avivco5/juckbox/design/4f1e619b-26d6-46fd-890a-413171e89c38.png

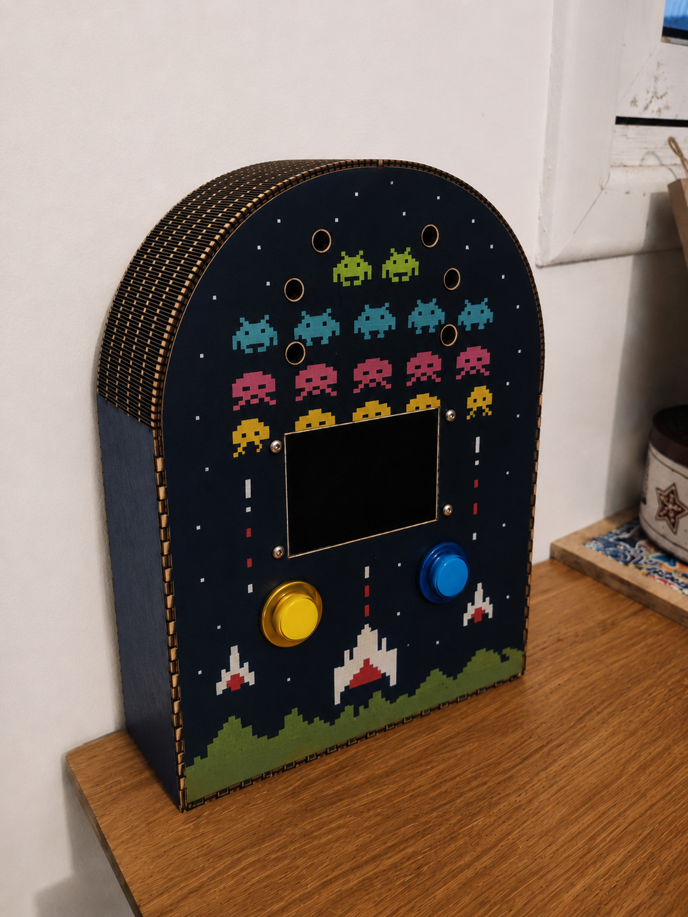
design/4f1e619b-26d6-46fd-890a-413171e89c38.png
