avivco5/juckbox/design/27ebfebb-9b08-406d-80b3-61969d63497d.png

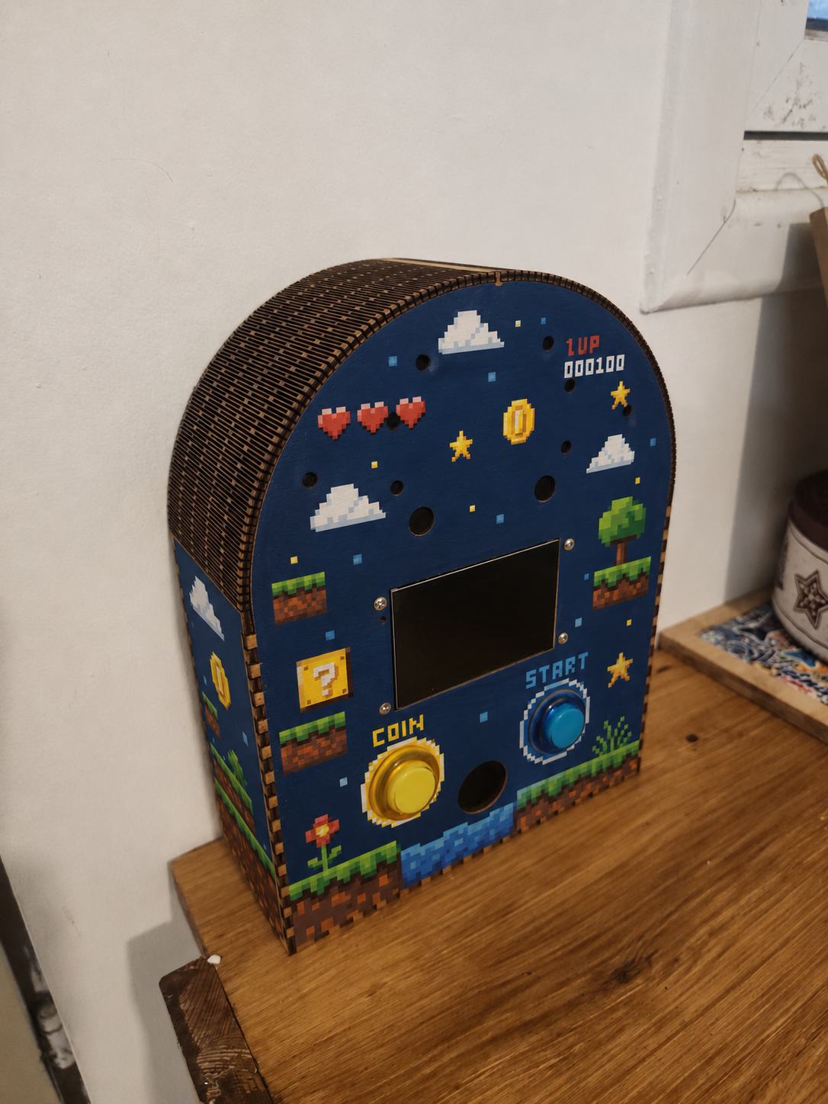
design/27ebfebb-9b08-406d-80b3-61969d63497d.png
