avivco5/juckbox/design/34f83e39-5371-48dc-b8f7-de62b93157a2.png

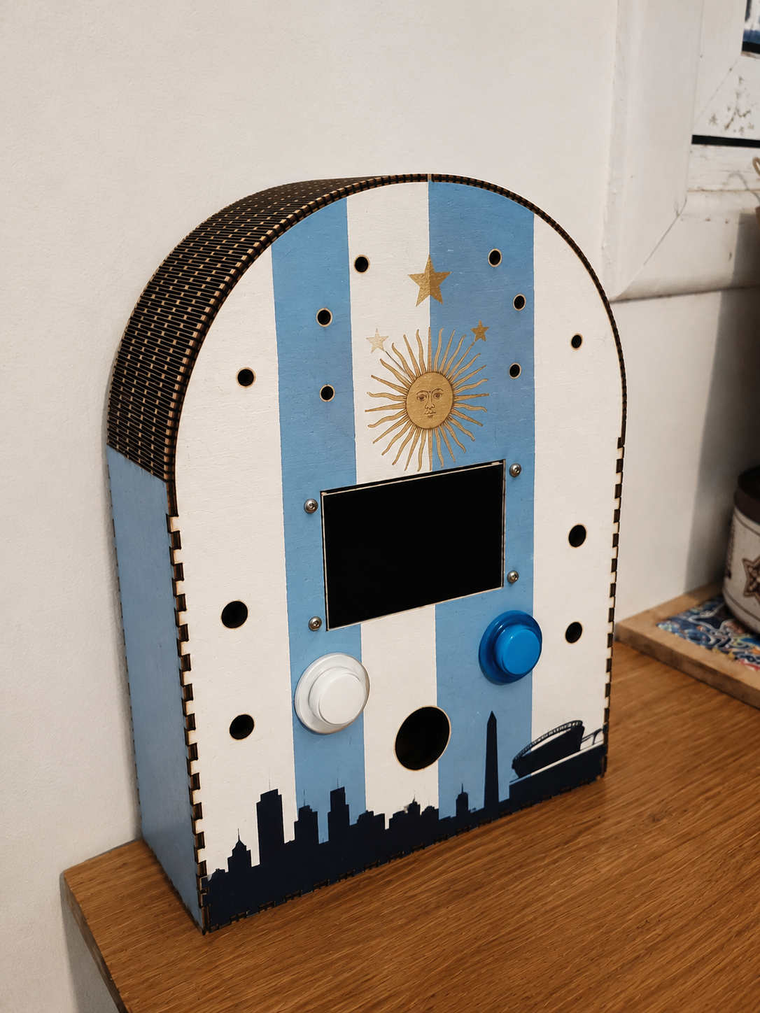
design/34f83e39-5371-48dc-b8f7-de62b93157a2.png
