avivco5/juckbox/design/97b78420-3eb2-440e-917a-7a141fbbd64f.png

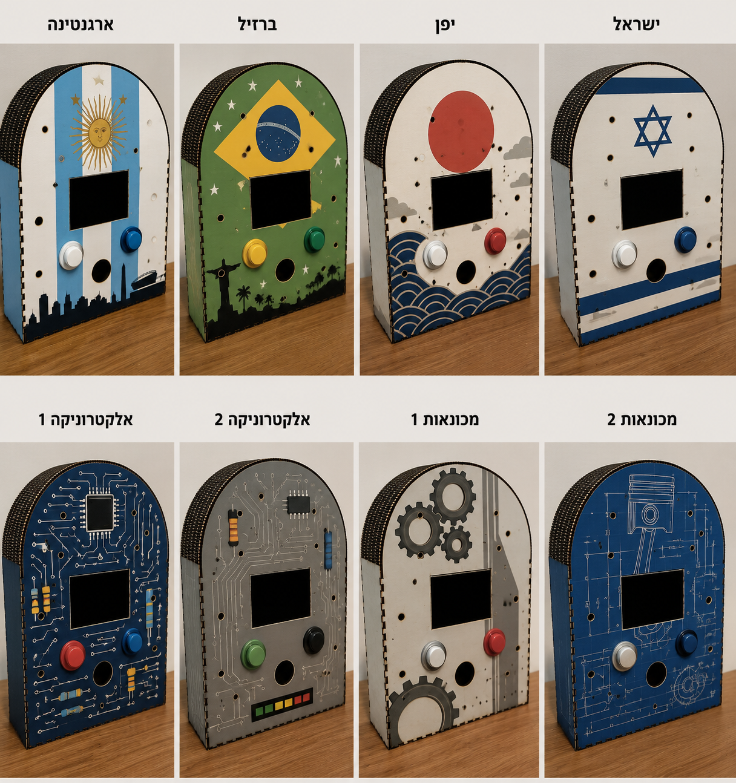
design/97b78420-3eb2-440e-917a-7a141fbbd64f.png
