avivco5/juckbox/design/892bf61c-9726-4b2f-9761-84908b169551.png

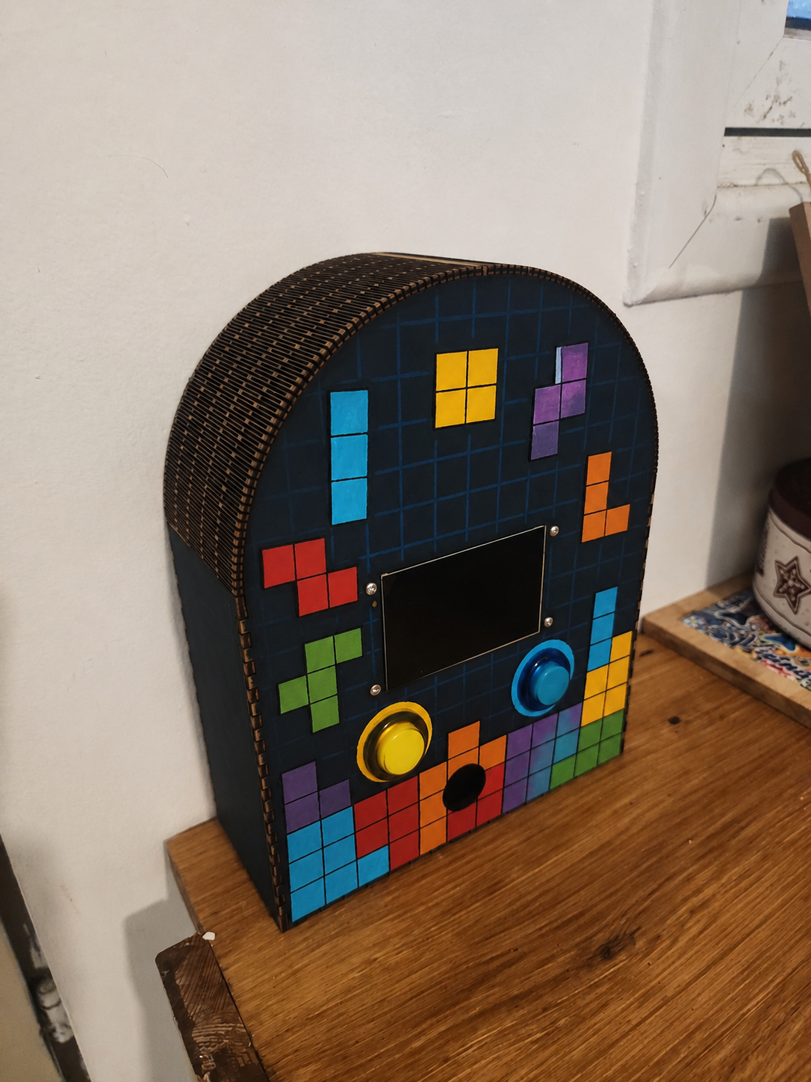
design/892bf61c-9726-4b2f-9761-84908b169551.png
