avivco5/juckbox/design/26971b3d-81b3-4ab2-a4b9-a8ff20f6ef65.png

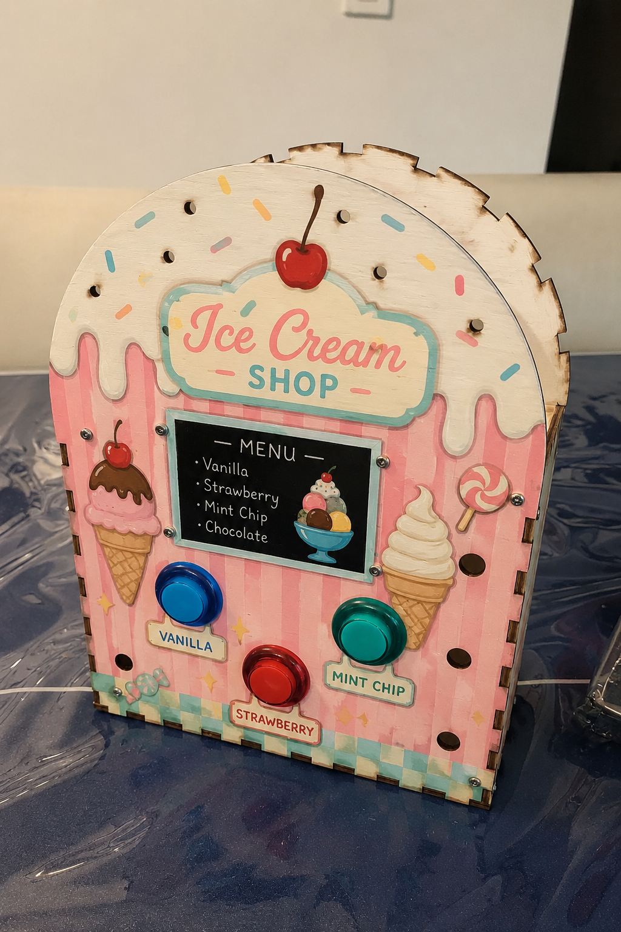
design/26971b3d-81b3-4ab2-a4b9-a8ff20f6ef65.png
