avivco5/juckbox/design/bb11b732-9e90-4e72-ab10-1f3d75999959.png

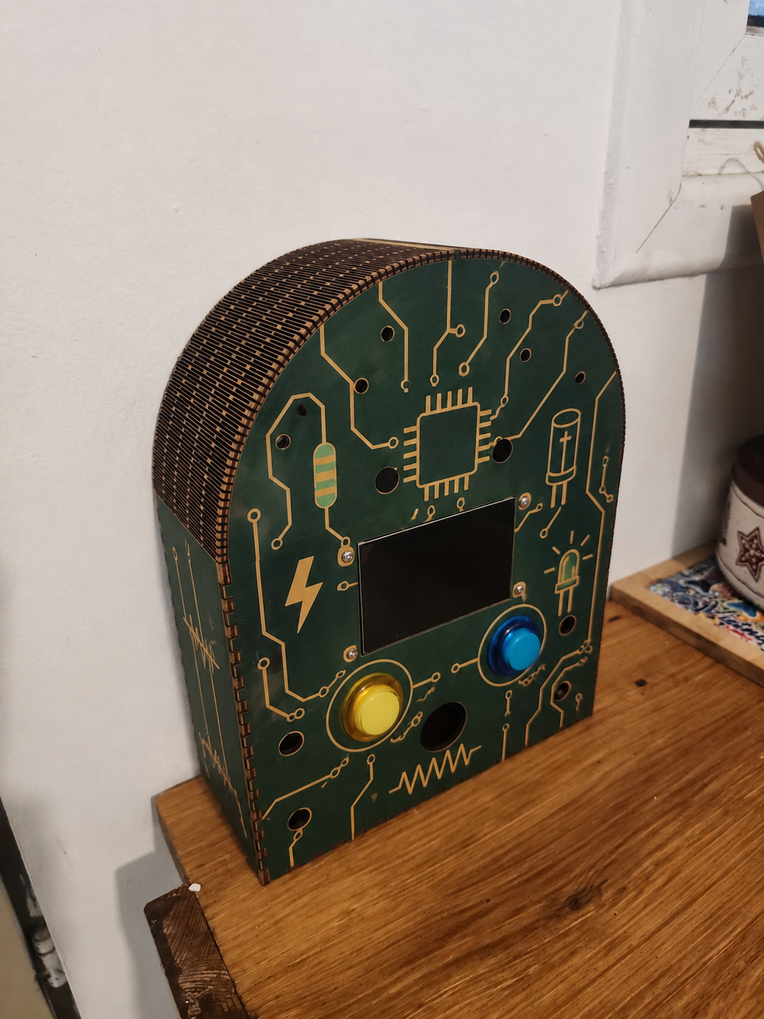
design/bb11b732-9e90-4e72-ab10-1f3d75999959.png
