avivco5/juckbox/design/ChatGPT Image Jul 7, 2026, 10_58_40 PM.png

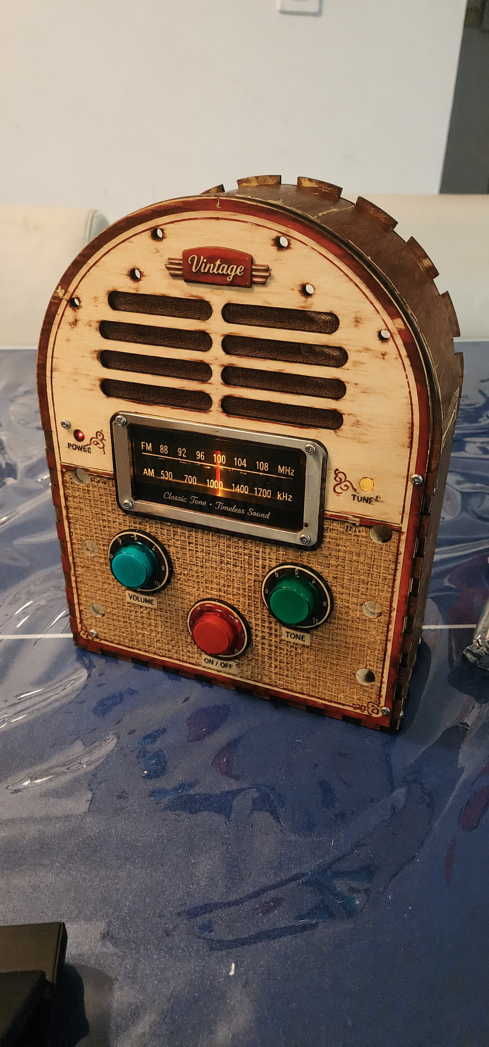
design/ChatGPT Image Jul 7, 2026, 10_58_40 PM.png
