avivco5/juckbox/design/ChatGPT Image Jul 7, 2026, 11_04_46 PM.png

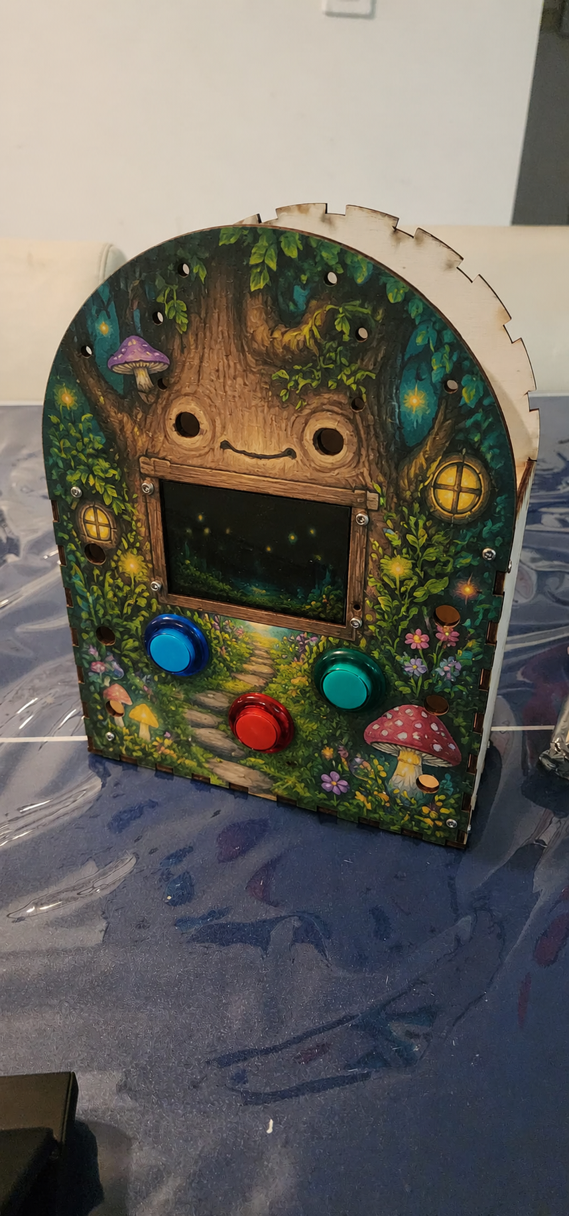
design/ChatGPT Image Jul 7, 2026, 11_04_46 PM.png
