avivco5/juckbox/design/ChatGPT Image Jul 11, 2026, 03_16_33 PM.png

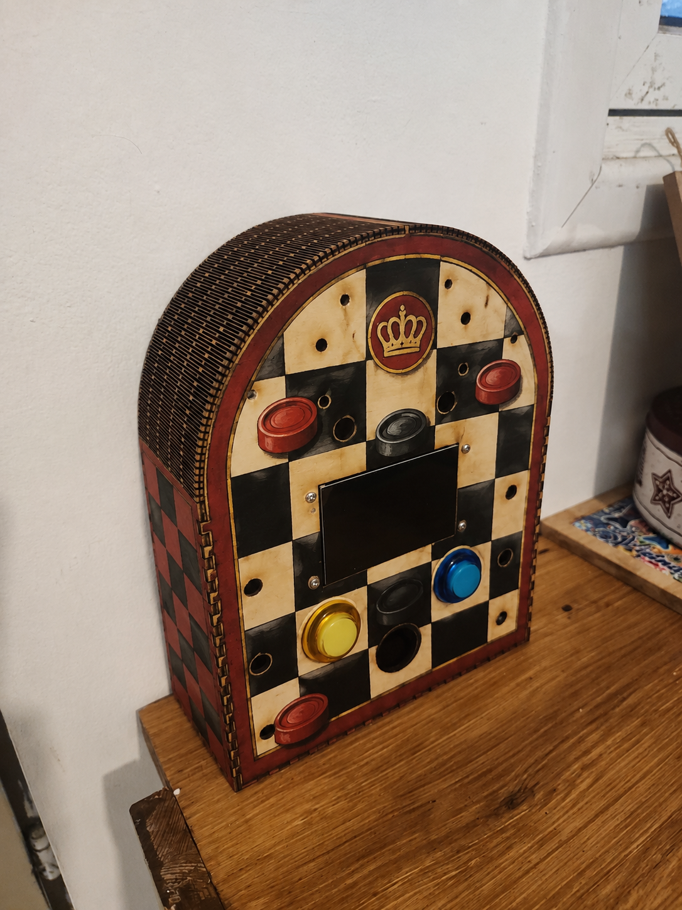
design/ChatGPT Image Jul 11, 2026, 03_16_33 PM.png
