avivco5/juckbox/design/ChatGPT Image Jul 13, 2026, 04_00_38 AM.png

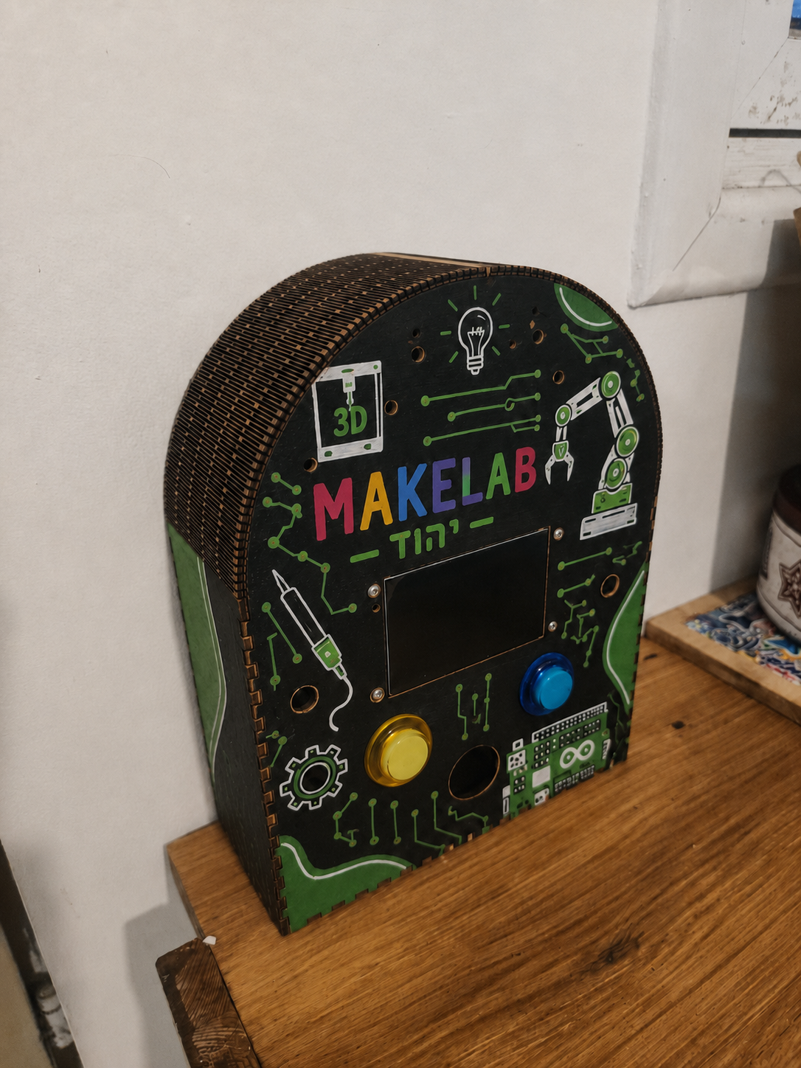
design/ChatGPT Image Jul 13, 2026, 04_00_38 AM.png
