avivco5/juckbox/design/d009f1e1-ca12-4269-a878-5f64a306e6af.png

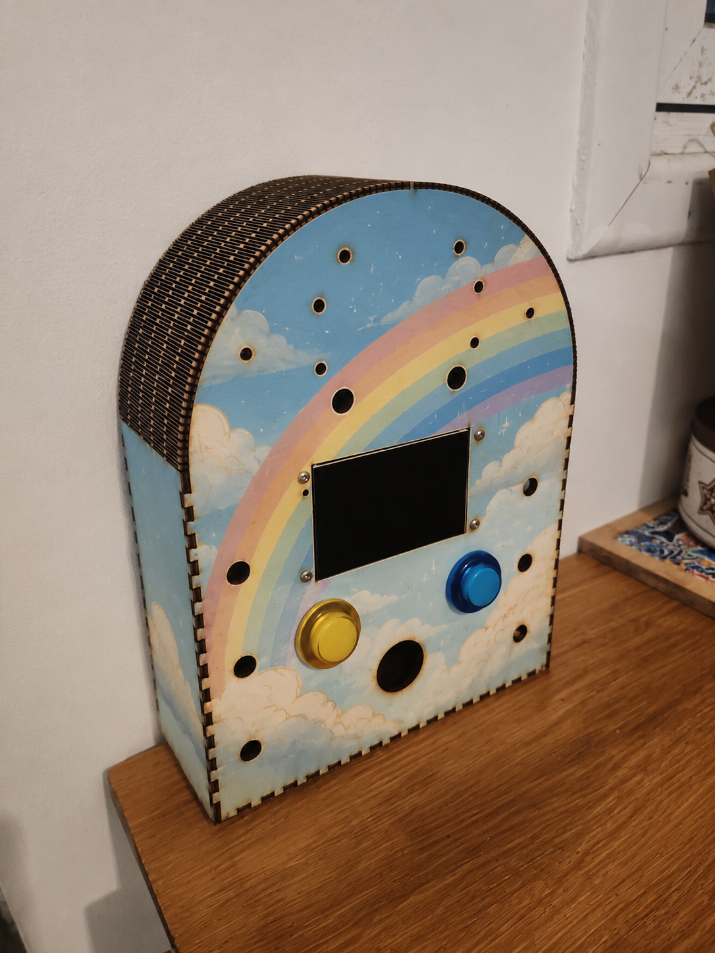
design/d009f1e1-ca12-4269-a878-5f64a306e6af.png
