avivco5/juckbox/design/f1ebbad3-cf48-4e45-876e-ef45e3f0cdeb.png

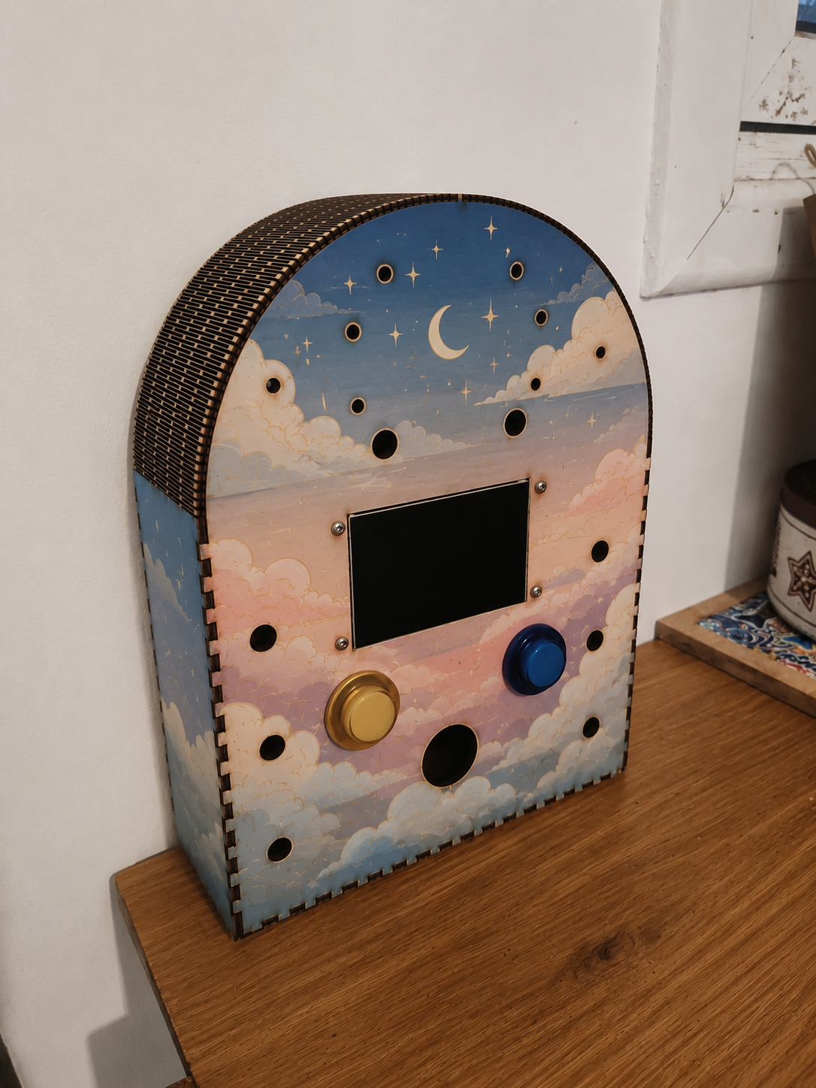
design/f1ebbad3-cf48-4e45-876e-ef45e3f0cdeb.png
