avivco5/juckbox/design/f6f87b5b-e072-4f04-99ac-8c54d5e9d249.png

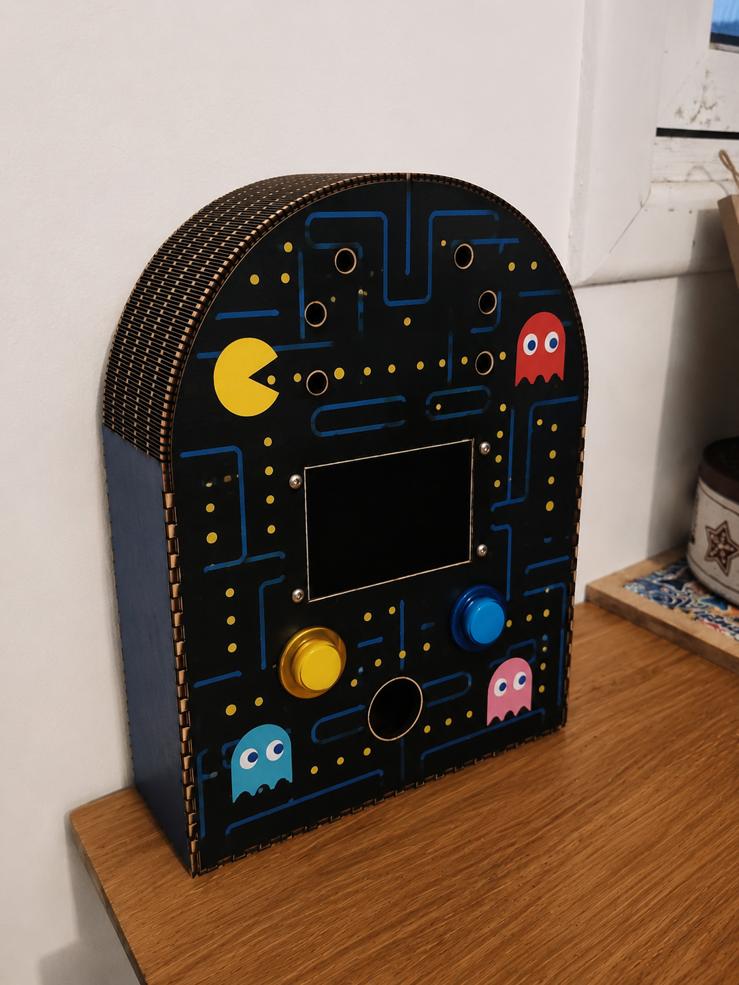
design/f6f87b5b-e072-4f04-99ac-8c54d5e9d249.png
