avivco5/juckbox/firmware/src/DisplayDriver.cpp

#include "DisplayDriver.h"

#include <algorithm>

namespace {
constexpr int LcdCs = 10;
constexpr int LcdClock = 12;
constexpr int LcdData0 = 11;
constexpr int LcdData1 = 13;
constexpr int LcdData2 = 14;
constexpr int LcdData3 = 9;
constexpr int LcdBacklight = 41;

constexpr int PanelWidth = 320;
constexpr int PanelHeight = 480;
constexpr int TransferColumns = 48;

// Format: command, data length, delay in milliseconds, data bytes.
// Vendor sequence for the QDTech/LCDWiki ES3C35P ST77922 panel.
const uint8_t PanelInit[] = {
    0xF1, 1, 0, 0x00,
    0x60, 3, 0, 0x00, 0x00, 0x00,
    0x65, 1, 0, 0x80,
    0x79, 1, 0, 0x06,
    0x7B, 3, 0, 0x00, 0x08, 0x08,
    0x80, 11, 0, 0x55, 0x62, 0x2F, 0x17, 0xF0, 0x52, 0x70, 0xD2, 0x52, 0x62, 0xEA,
    0x81, 4, 0, 0x26, 0x52, 0x72, 0x27,
    0x84, 2, 0, 0x92, 0x25,
    0x87, 6, 0, 0x10, 0x10, 0x58, 0x00, 0x02, 0x3A,
    0x88, 15, 0, 0x00, 0x00, 0x2C, 0x10, 0x04, 0x00, 0x00, 0x00, 0x01, 0x01, 0x01, 0x01, 0x01, 0x00, 0x06,
    0x89, 3, 0, 0x00, 0x00, 0x00,
    0x8A, 11, 0, 0x13, 0x00, 0x2C, 0x00, 0x00, 0x2C, 0x10, 0x10, 0x00, 0x3E, 0x19,
    0x8B, 9, 0, 0x15, 0xB1, 0xB1, 0x44, 0x96, 0x2C, 0x10, 0x97, 0x8E,
    0x8C, 13, 0, 0x1D, 0xB1, 0xB1, 0x44, 0x96, 0x2C, 0x10, 0x50, 0x0F, 0x01, 0xC5, 0x12, 0x09,
    0x8D, 1, 0, 0x0C,
    0x8E, 6, 0, 0x33, 0x01, 0x0C, 0x13, 0x01, 0x01,
    0xB3, 2, 0, 0x00, 0x30,
    0xF1, 1, 0, 0x00,
    0x71, 1, 0, 0xD0,
    0x66, 2, 0, 0x02, 0x3F,
    0xBE, 3, 0, 0x26, 0x00, 0x9D,
    0x70, 12, 0, 0x01, 0xA0, 0x11, 0x40, 0xE0, 0x00, 0x11, 0x69, 0x11, 0x00, 0x00, 0x1A,
    0x90, 9, 0, 0x04, 0x04, 0x55, 0x74, 0x00, 0x40, 0x43, 0x27, 0x27,
    0x91, 9, 0, 0x04, 0x04, 0x55, 0x75, 0x00, 0x40, 0x42, 0x27, 0x27,
    0x92, 10, 0, 0x04, 0x44, 0x55, 0xC0, 0x06, 0x00, 0x07, 0x05, 0x90, 0x27,
    0x93, 10, 0, 0x04, 0x43, 0x11, 0x00, 0x00, 0x00, 0x00, 0x05, 0x90, 0x27,
    0x94, 6, 0, 0x00, 0x00, 0x00, 0x00, 0x00, 0x00,
    0x95, 5, 0, 0x96, 0x16, 0x00, 0x00, 0xFF,
    0x96, 12, 0, 0x44, 0x53, 0x03, 0x12, 0x23, 0x24, 0x06, 0x05, 0x94, 0x27, 0x00, 0x44,
    0x97, 12, 0, 0x44, 0x53, 0x47, 0x56, 0x20, 0x20, 0x02, 0x01, 0x94, 0x27, 0x00, 0x44,
    0xBA, 5, 0, 0x55, 0x94, 0x2D, 0x94, 0x27,
    0x9A, 7, 0, 0x40, 0x00, 0x06, 0x00, 0x00, 0x00, 0x00,
    0x9B, 7, 0, 0x00, 0x00, 0x06, 0x00, 0x00, 0x00, 0x00,
    0x9C, 13, 0, 0x5C, 0x12, 0x00, 0x00, 0x10, 0x12, 0x00, 0x00, 0x10, 0x02, 0x00, 0x00, 0x00,
    0x9D, 8, 0, 0x8A, 0x51, 0x00, 0x00, 0x00, 0x80, 0x1E, 0x01,
    0x9E, 7, 0, 0x51, 0x00, 0x00, 0x00, 0x80, 0x1E, 0x01,
    0xB4, 12, 0, 0x1D, 0x1C, 0x1E, 0x0B, 0x14, 0x02, 0x13, 0x09, 0x1E, 0x00, 0x1E, 0x10,
    0xB5, 12, 0, 0x1D, 0x1C, 0x1E, 0x0A, 0x15, 0x03, 0x11, 0x08, 0x1E, 0x01, 0x1E, 0x12,
    0xB6, 7, 0, 0x77, 0x77, 0x00, 0x0A, 0xFF, 0x0A, 0xFF,
    0x86, 14, 0, 0xCD, 0x04, 0xB1, 0x02, 0x58, 0x12, 0x58, 0x0C, 0x13, 0x01, 0xA5, 0x00, 0xA5, 0xA5,
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
};
}

DisplayDriver displayDriver;

bool DisplayDriver::begin()
{
    setBacklight(true);

    _bus = new Arduino_ESP32QSPI(
        LcdCs, LcdClock, LcdData0, LcdData1, LcdData2, LcdData3);
    if (!_bus || !_bus->begin(40000000))
    {
        return false;
    }

    initializePanel();

    _canvas = new Arduino_Canvas(Width, Height, nullptr);
    if (!_canvas || !_canvas->begin(GFX_SKIP_OUTPUT_BEGIN))
    {
        return false;
    }

    _transferBuffer = static_cast<uint16_t*>(
        heap_caps_malloc(
            PanelWidth * TransferColumns * sizeof(uint16_t),
            MALLOC_CAP_DMA | MALLOC_CAP_8BIT));

    return _transferBuffer != nullptr;
}

void DisplayDriver::setBacklight(bool enabled)
{
    pinMode(LcdBacklight, OUTPUT);
    digitalWrite(LcdBacklight, enabled ? HIGH : LOW);
}

void DisplayDriver::sendCommand(
    uint8_t command,
    const uint8_t* data,
    uint8_t length)
{
    if (length == 0)
    {
        _bus->sendCommand(command);
        return;
    }

    _bus->writeC8Bytes(
        command,
        const_cast<uint8_t*>(data),
        length);
}

void DisplayDriver::initializePanel()
{
    _bus->sendCommand(0x01);
    delay(120);

    const uint8_t madctl = 0x00;
    const uint8_t colorMode = 0x55;
    sendCommand(0x36, &madctl, 1);
    sendCommand(0x3A, &colorMode, 1);

    const uint8_t* cursor = PanelInit;
    const uint8_t* end = PanelInit + sizeof(PanelInit);
    while (cursor < end)
    {
        const uint8_t command = *cursor++;
        const uint8_t length = *cursor++;
        const uint8_t delayMs = *cursor++;
        sendCommand(command, cursor, length);
        cursor += length;

        if (delayMs)
        {
            delay(delayMs);
        }
    }
}

void DisplayDriver::flush()
{
    if (!_canvas || !_transferBuffer)
    {
        return;
    }

    const uint16_t* source = _canvas->getFramebuffer();

    for (int landscapeX = 0; landscapeX < Width; landscapeX += TransferColumns)
    {
        const int columns = std::min(TransferColumns, Width - landscapeX);

        for (int localX = 0; localX < columns; ++localX)
        {
            for (int landscapeY = 0; landscapeY < Height; ++landscapeY)
            {
                _transferBuffer[localX * Height + (Height - landscapeY - 1)] =
                    source[landscapeY * Width + landscapeX + localX];
            }
        }

        _bus->writeC8D16D16(0x2A, 0, PanelWidth - 1);
        _bus->writeC8D16D16(
            0x2B,
            landscapeX,
            landscapeX + columns - 1);
        _bus->sendCommand(0x2C);
        _bus->writePixels(
            _transferBuffer,
            PanelWidth * columns);
    }
}
